niclasku/rpi-timeclock-terminal/data/empty.jpg

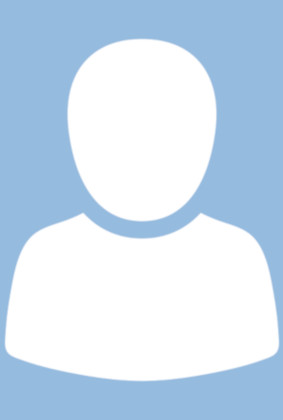
data/empty.jpg
