niclasku/rpi-timeclock-terminal/images/clockin.png

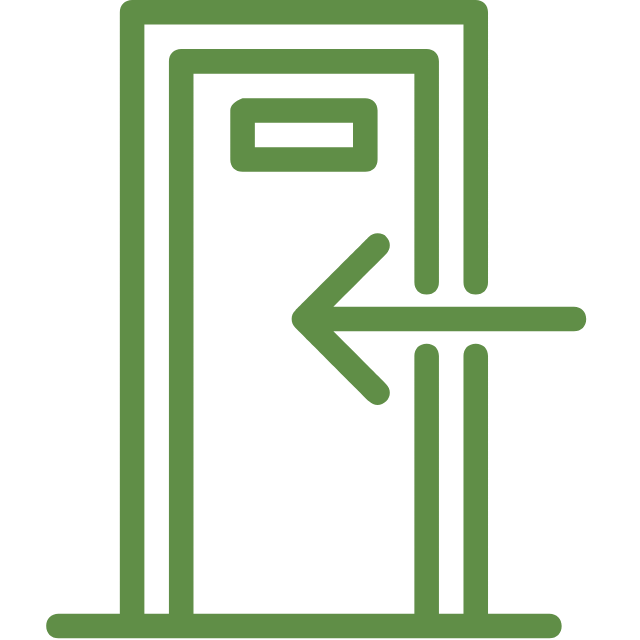
images/clockin.png
